maynej/Grua-Portuaria-Stemfie/Imatges/Carret28BYJ-48.png

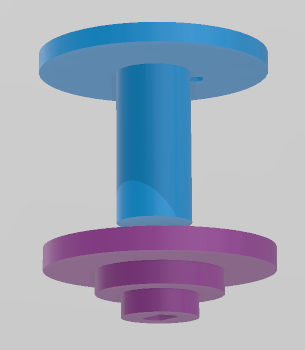
Imatges/Carret28BYJ-48.png
