maynej/Grua-Portuaria-Stemfie/Imatges/IMG_20220824_123127_317.jpg

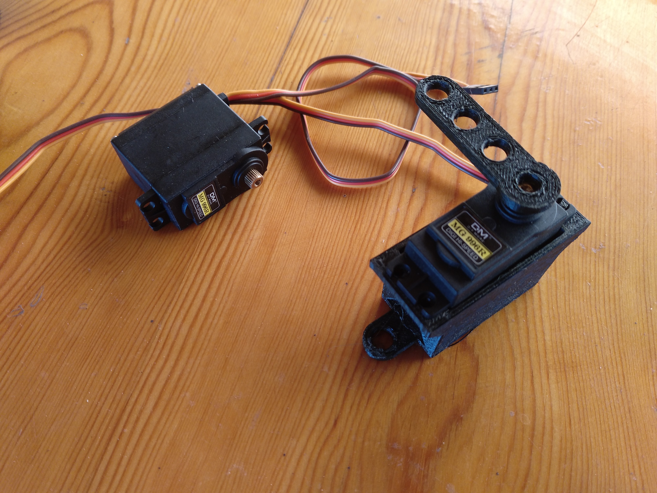
Imatges/IMG_20220824_123127_317.jpg
