maynej/Grua-Portuaria-Stemfie/STL/Base/28BYJ-48_2H_Stemfie_x1.stl

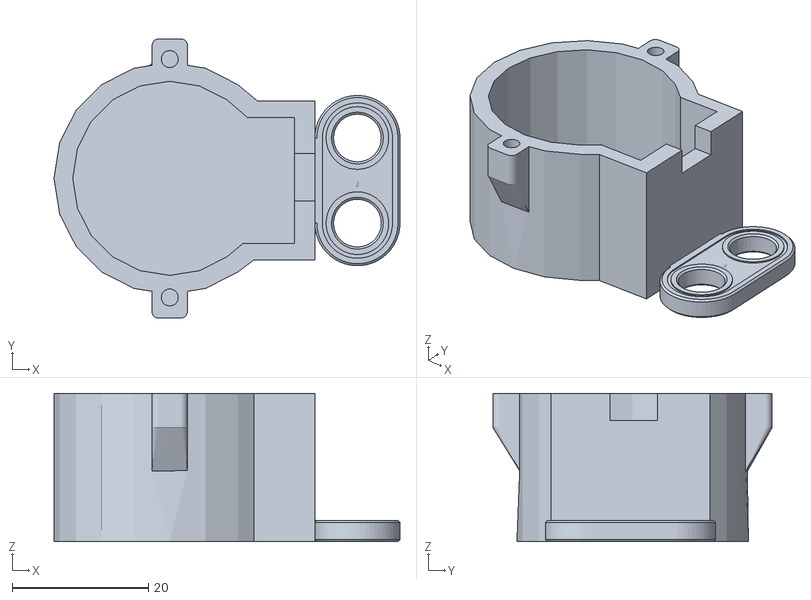
[picture p64: CAD file, 2022-09-06]
STL/Base/28BYJ-48_2H_Stemfie_x1.stl
50.8 x 41.0 x 21.8
