maynej/Grua-Portuaria-Stemfie/STL/PlataformaGiratoria/EngranatgeGrua_x1.stl

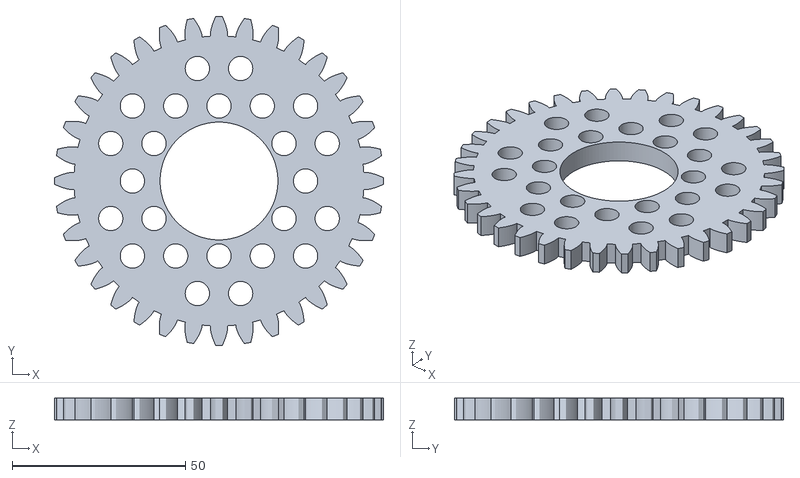
[picture p65: CAD file, 2022-09-06]
STL/PlataformaGiratoria/EngranatgeGrua_x1.stl
95.0 x 95.0 x 6.25
