maynej/Grua-Portuaria-Stemfie/STL/Ploma/PinBU03.75_x1.stl

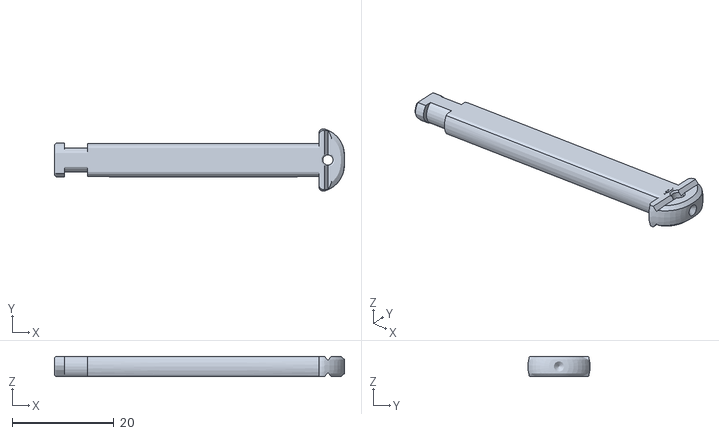
[picture p66: CAD file, 2022-09-06]
STL/Ploma/PinBU03.75_x1.stl
56.9 x 12.2 x 4.00
