maynej/Grua-Portuaria-Stemfie/STL/Base/Spool28BYJ-48_1.stl

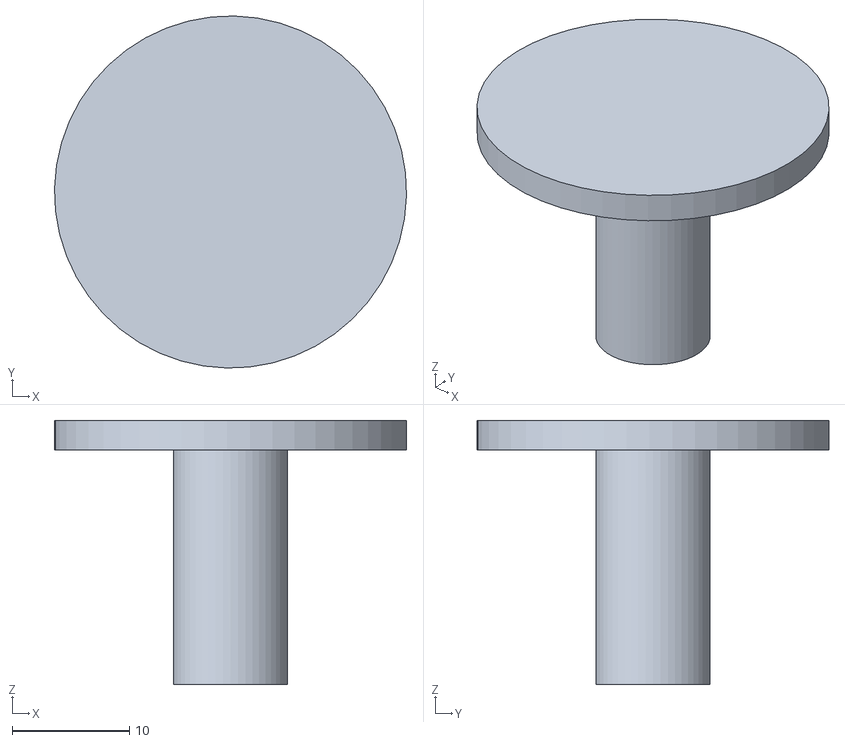
[picture p67: CAD file, 2022-09-06]
STL/Base/Spool28BYJ-48_1.stl
30.0 x 30.0 x 22.5
