maynej/Grua-Portuaria-Stemfie/STL/Ploma/Brace2_x8.stl

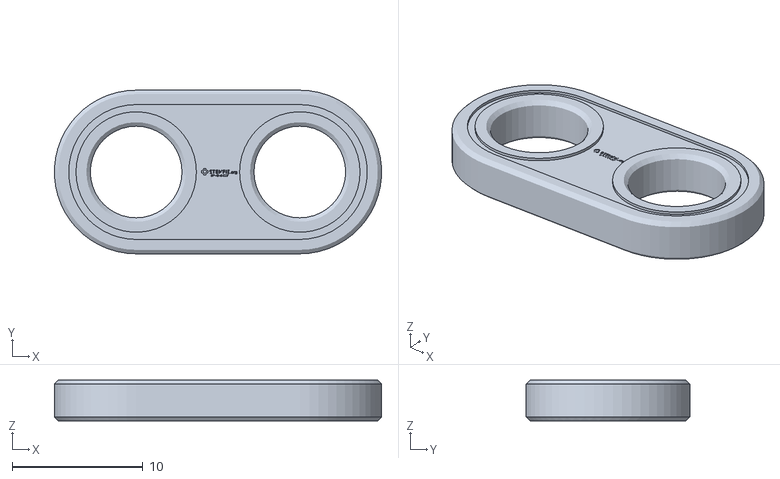
[picture p68: CAD file, 2022-09-06]
STL/Ploma/Brace2_x8.stl
25.0 x 12.5 x 3.12
