maynej/Grua-Portuaria-Stemfie/STL/Base/Brace18_x4.stl

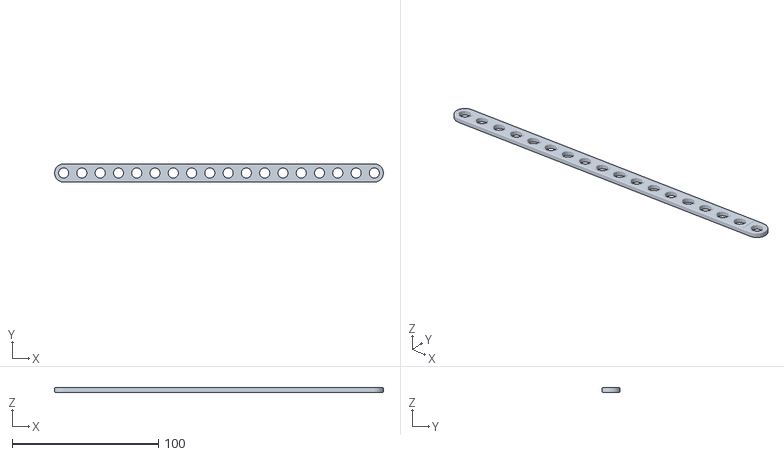
[picture p69: CAD file, 2022-09-06]
STL/Base/Brace18_x4.stl
225.0 x 12.5 x 3.12
