maynej/Grua-Portuaria-Stemfie/STL/Ploma/PulleyBU1.00_x3.stl

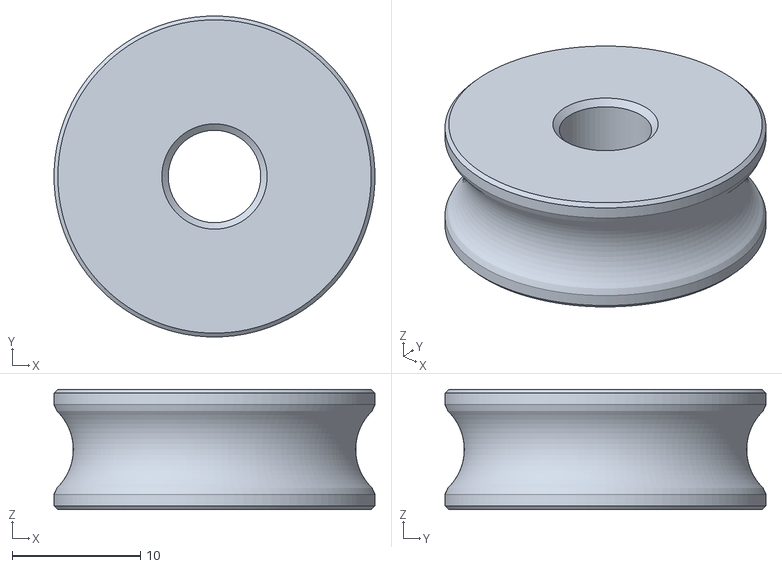
[picture p70: CAD file, 2022-09-06]
STL/Ploma/PulleyBU1.00_x3.stl
25.0 x 25.0 x 9.38
