maynej/Grua-Portuaria-Stemfie/STL/Base/Base8x10_x1.stl

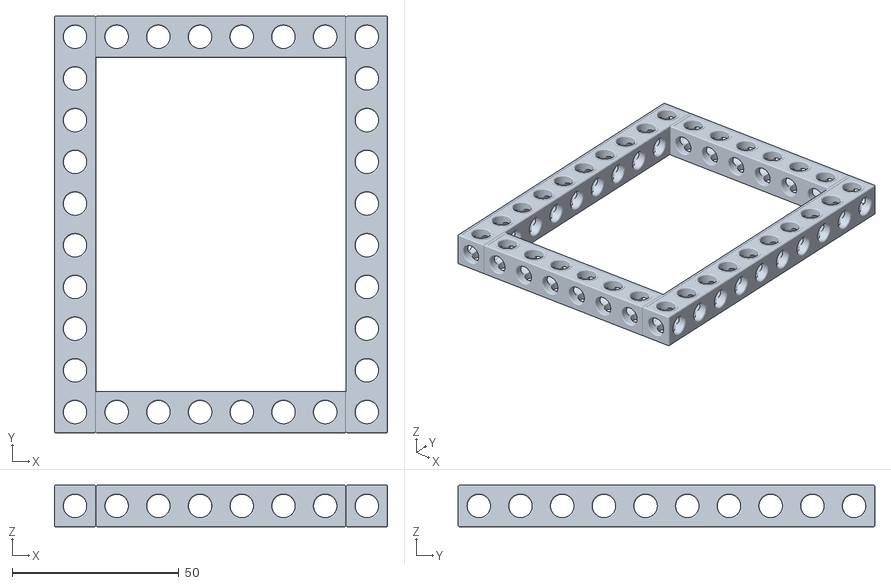
[picture p71: CAD file, 2022-09-06]
STL/Base/Base8x10_x1.stl
100.0 x 125.0 x 12.5
