maynej/Grua-Portuaria-Stemfie/STL/Ploma/Beam5_x2.stl

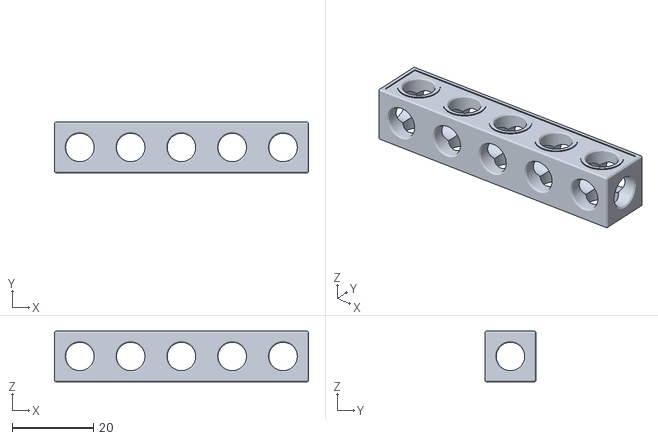
[picture p72: CAD file, 2022-09-06]
STL/Ploma/Beam5_x2.stl
62.5 x 12.5 x 12.5
