maynej/Grua-Portuaria-Stemfie/STL/Base/28BYJ-48_4H_Stemfie_x1.stl

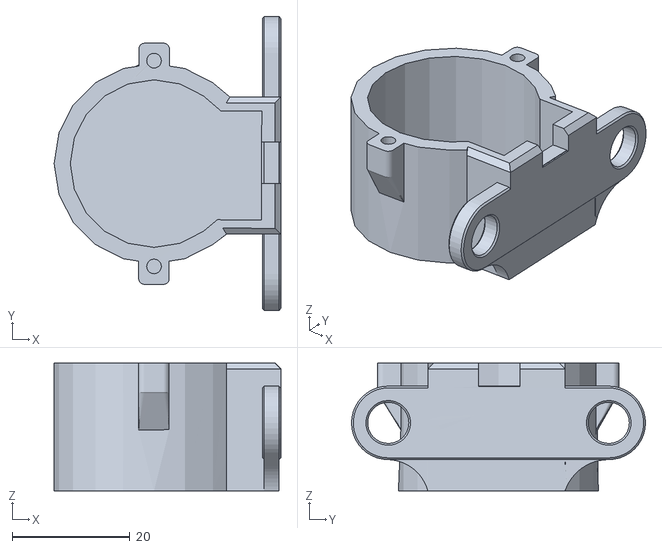
[picture p73: CAD file, 2022-09-06]
STL/Base/28BYJ-48_4H_Stemfie_x1.stl
38.6 x 50.0 x 21.8
