maynej/Grua-Portuaria-Stemfie/STL/Ploma/ServoMG966_V3_x2.stl

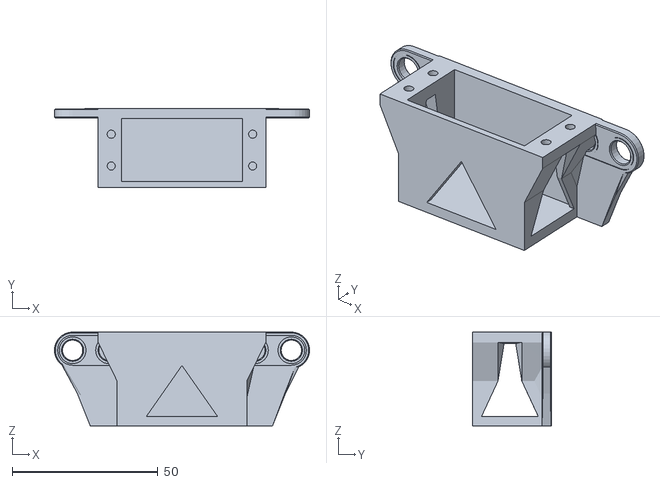
[picture p74: CAD file, 2022-09-06]
STL/Ploma/ServoMG966_V3_x2.stl
87.4 x 26.9 x 32.2
