maynej/Grua-Portuaria-Stemfie/STL/Base/Arandela2.5mm_x4.stl

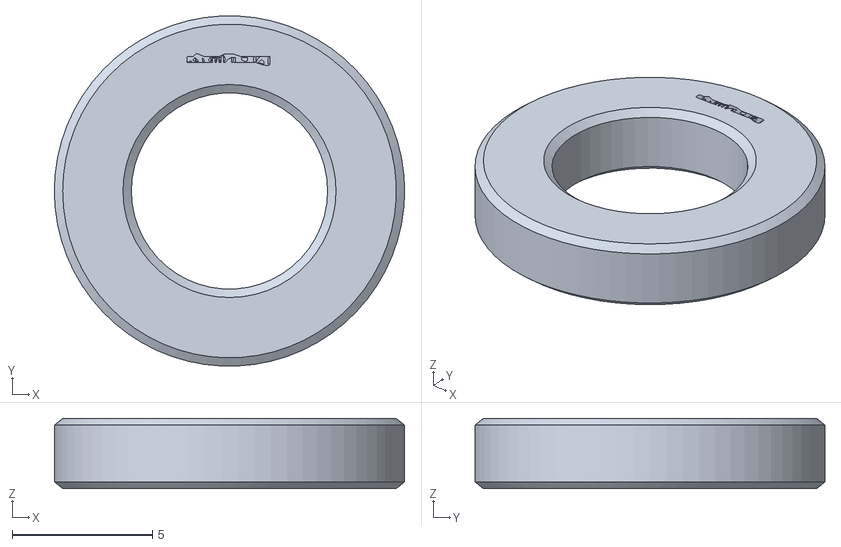
[picture p75: CAD file, 2022-09-06]
STL/Base/Arandela2.5mm_x4.stl
12.5 x 12.5 x 2.51
