maynej/Grua-Portuaria-Stemfie/STL/Base/Gear28BYJ-48_130mm_x1.stl

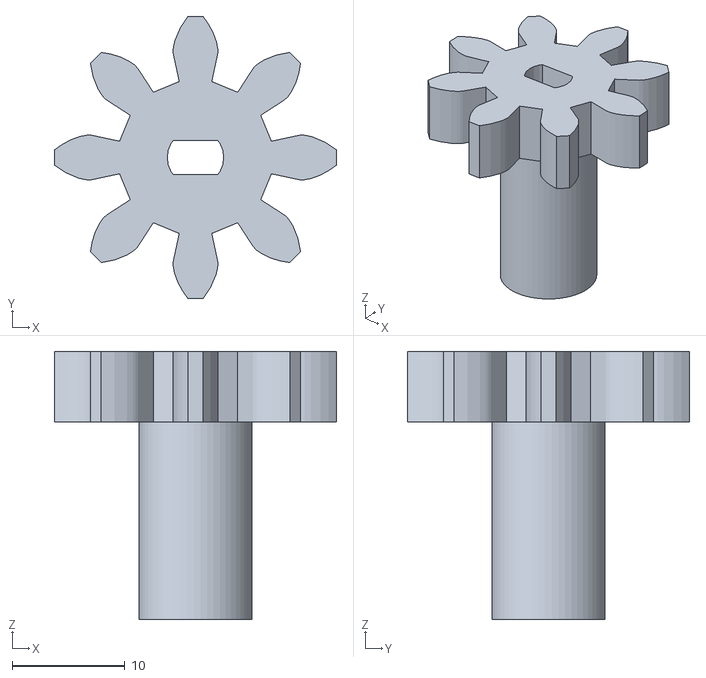
[picture p76: CAD file, 2022-09-06]
STL/Base/Gear28BYJ-48_130mm_x1.stl
25.0 x 25.0 x 23.8
