maynej/Grua-Portuaria-Stemfie/STL/Base/Brace13_x4.stl

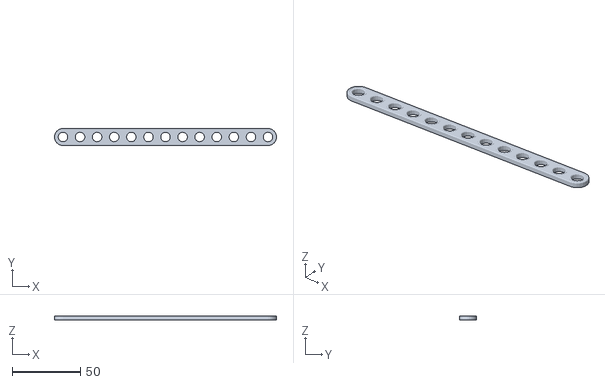
[picture p77: CAD file, 2022-09-06]
STL/Base/Brace13_x4.stl
162.4 x 12.5 x 3.12
