maynej/Grua-Portuaria-Stemfie/STL/Base/STR_STD_BRM-4x3_x1.stl

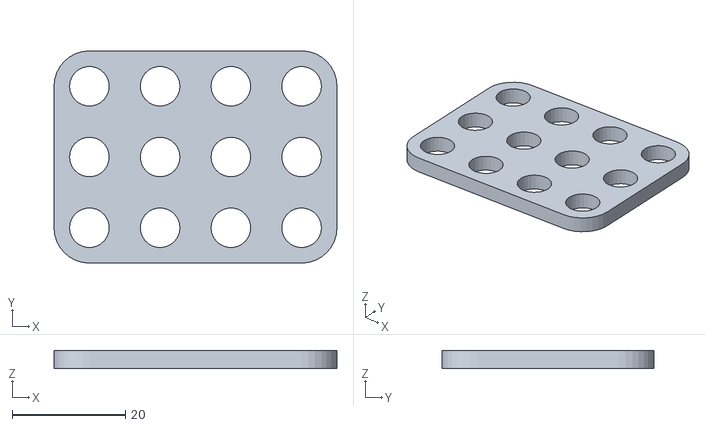
[picture p78: CAD file, 2022-09-06]
STL/Base/STR_STD_BRM-4x3_x1.stl
50.0 x 37.5 x 3.25
