maynej/Grua-Portuaria-Stemfie/STL/Ploma/Brace4_x6.stl

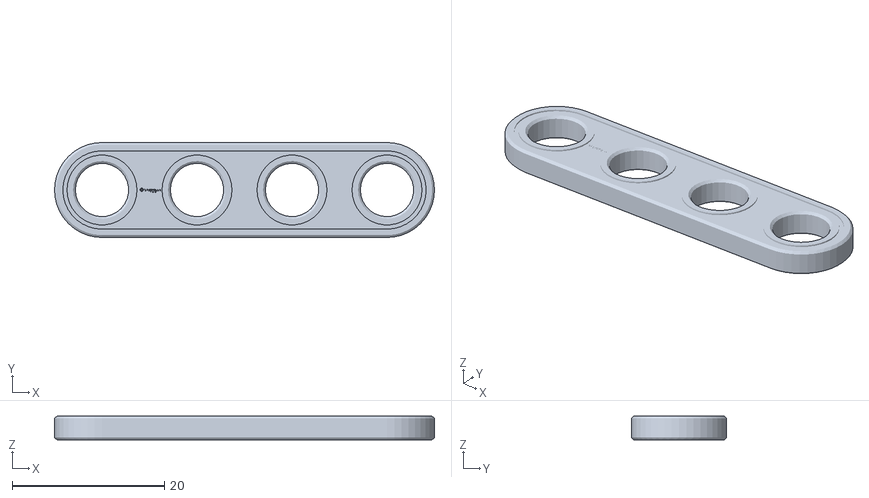
[picture p79: CAD file, 2022-09-06]
STL/Ploma/Brace4_x6.stl
50.0 x 12.5 x 3.12
