maynej/Grua-Portuaria-Stemfie/STL/Ploma/Brace6_x3.stl

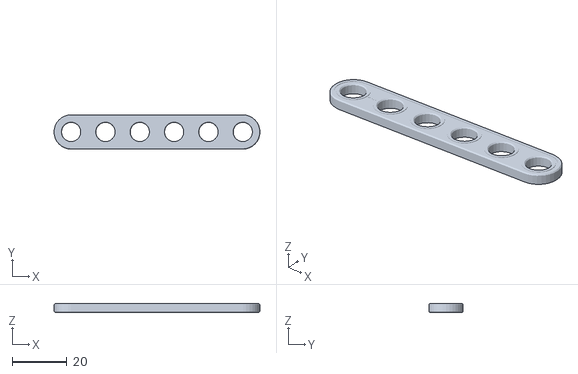
[picture p80: CAD file, 2022-09-06]
STL/Ploma/Brace6_x3.stl
75.0 x 12.5 x 3.12
