maynej/Grua-Portuaria-Stemfie/STL/Ploma/PinBU02.50_x4.stl

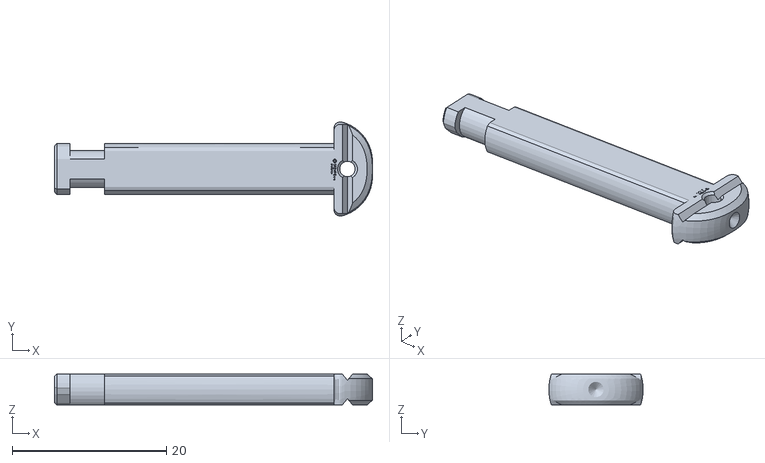
[picture p81: CAD file, 2022-09-06]
STL/Ploma/PinBU02.50_x4.stl
41.2 x 12.2 x 4.00
