maynej/Grua-Portuaria-Stemfie/STL/Ploma/Beam6x2_x1.stl

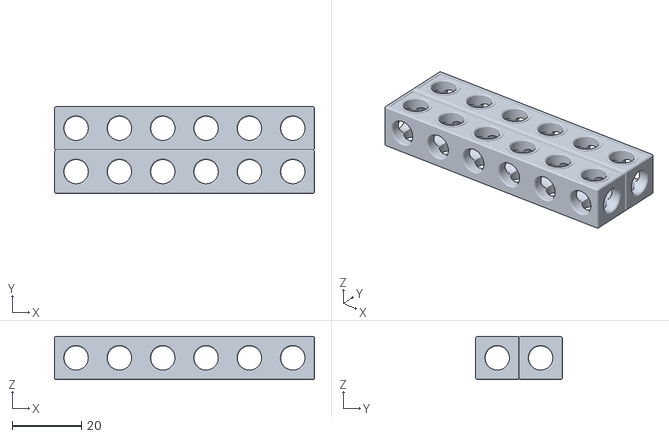
[picture p82: CAD file, 2022-09-06]
STL/Ploma/Beam6x2_x1.stl
75.0 x 25.0 x 12.5
