maynej/Grua-Portuaria-Stemfie/STL/Ploma/Brace12_x2.stl

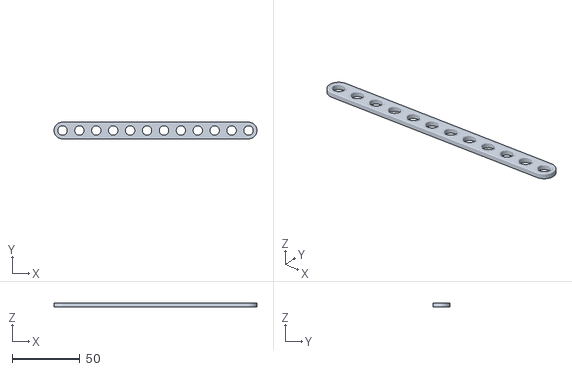
[picture p83: CAD file, 2022-09-06]
STL/Ploma/Brace12_x2.stl
150.0 x 12.5 x 3.12
