maynej/Grua-Portuaria-Stemfie/STL/Ploma/PinBU05.75_x1.stl

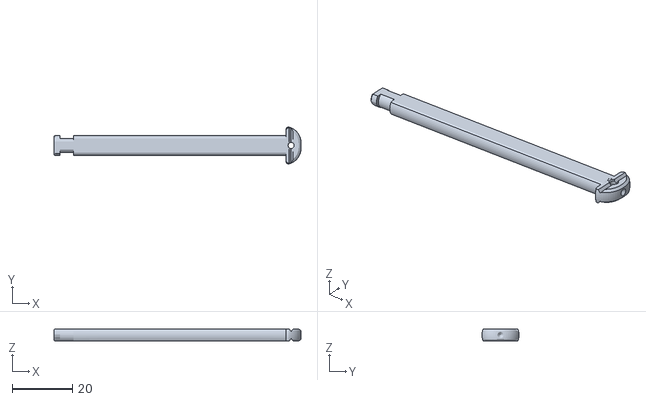
[picture p84: CAD file, 2022-09-06]
STL/Ploma/PinBU05.75_x1.stl
81.9 x 12.3 x 4.00
