maynej/Grua-Portuaria-Stemfie/STL/Ploma/PinBU01.75_x4.stl

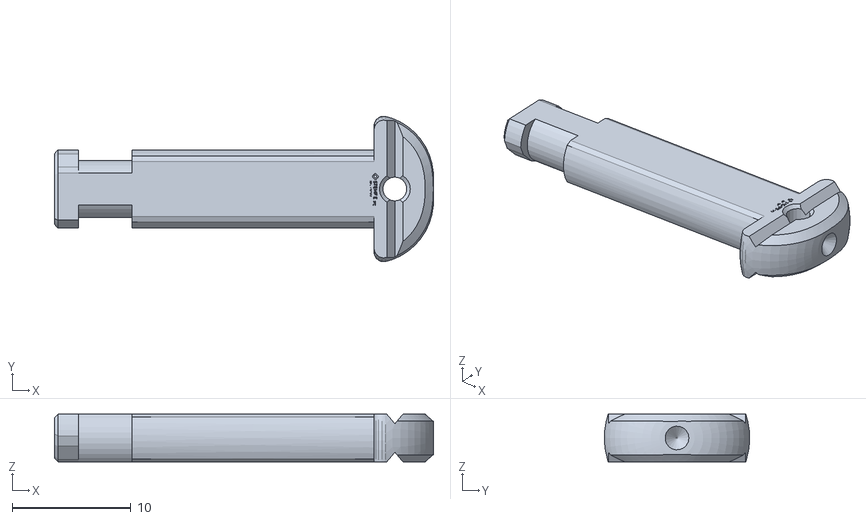
[picture p85: CAD file, 2022-09-06]
STL/Ploma/PinBU01.75_x4.stl
31.9 x 12.2 x 4.00
