maynej/Grua-Portuaria-Stemfie/STL/Ploma/Beam14_x3.stl

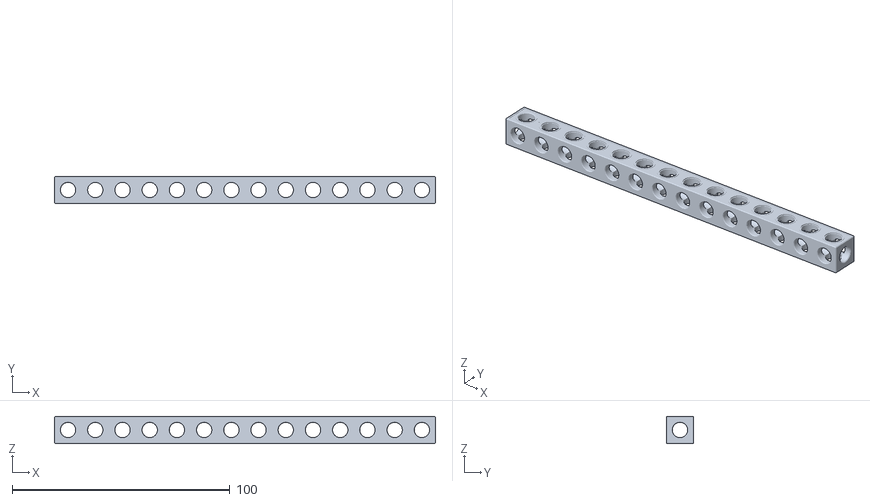
[picture p86: CAD file, 2022-09-06]
STL/Ploma/Beam14_x3.stl
175.0 x 12.5 x 12.5
