maynej/Grua-Portuaria-Stemfie/STL/Ploma/ServoMG996_Brace4_x2.stl

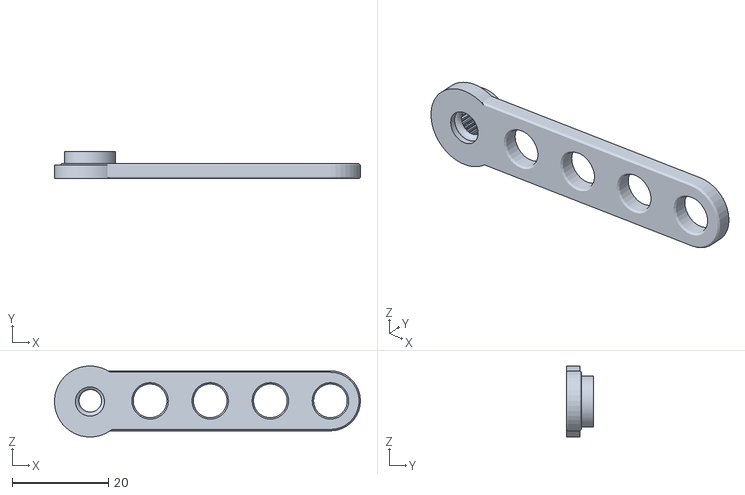
[picture p87: CAD file, 2022-09-06]
STL/Ploma/ServoMG996_Brace4_x2.stl
63.6 x 5.68 x 14.8
