maynej/Grua-Portuaria-Stemfie/STL/Ploma/NutFixed_x17.stl

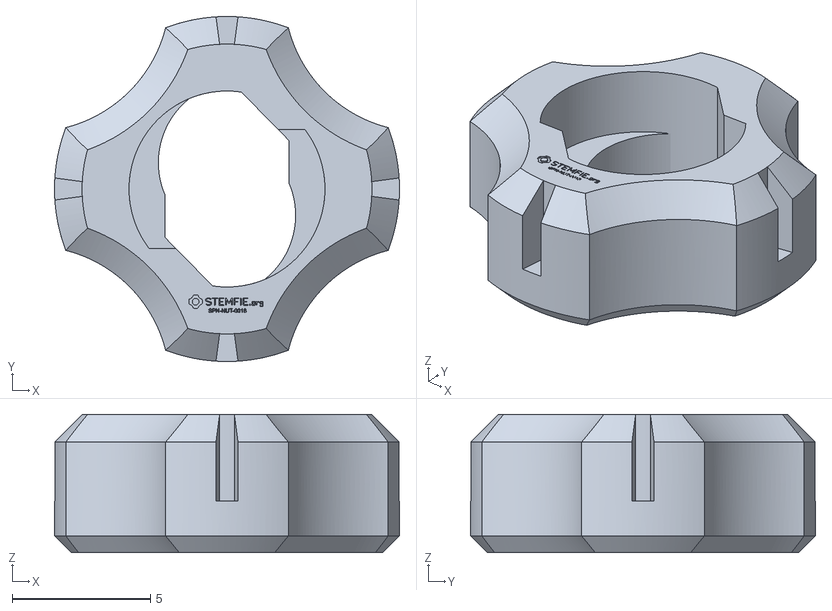
[picture p88: CAD file, 2022-09-06]
STL/Ploma/NutFixed_x17.stl
12.5 x 12.5 x 5.00
