maynej/Grua-Portuaria-Stemfie/STL/Ploma/Beam3_x1.stl

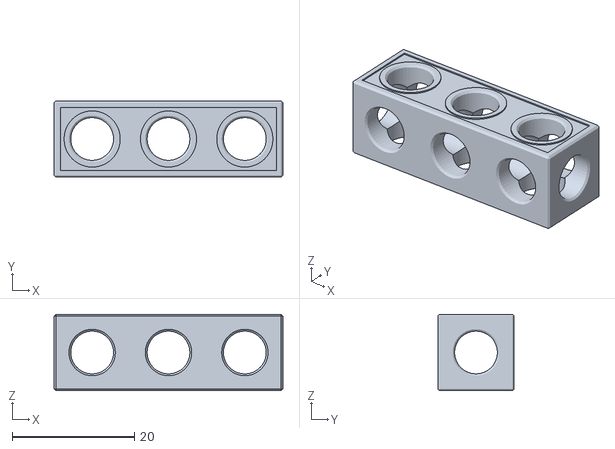
[picture p89: CAD file, 2022-09-06]
STL/Ploma/Beam3_x1.stl
37.5 x 12.5 x 12.5
