maynej/Grua-Portuaria-Stemfie/STL/Ploma/Beam18_x2.stl

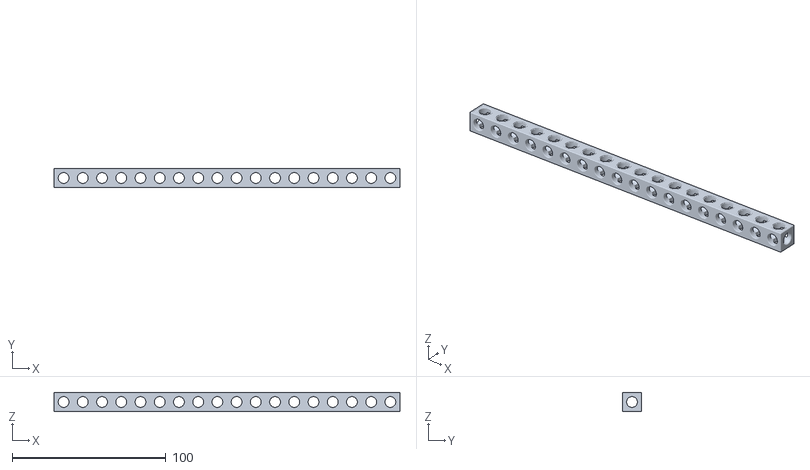
[picture p90: CAD file, 2022-09-06]
STL/Ploma/Beam18_x2.stl
225.0 x 12.5 x 12.5
