maynej/Grua-Portuaria-Stemfie/STL/Ploma/PinBU01.50_x16.stl

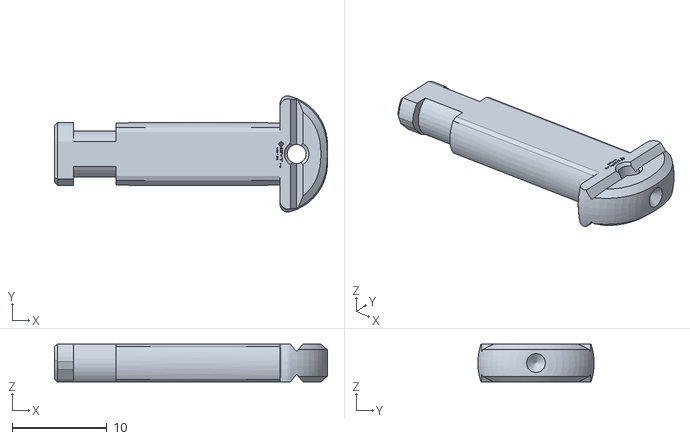
[picture p91: CAD file, 2022-09-06]
STL/Ploma/PinBU01.50_x16.stl
28.8 x 12.3 x 4.00
