maynej/Grua-Portuaria-Stemfie/STL/Ploma/Beam4_x1.stl

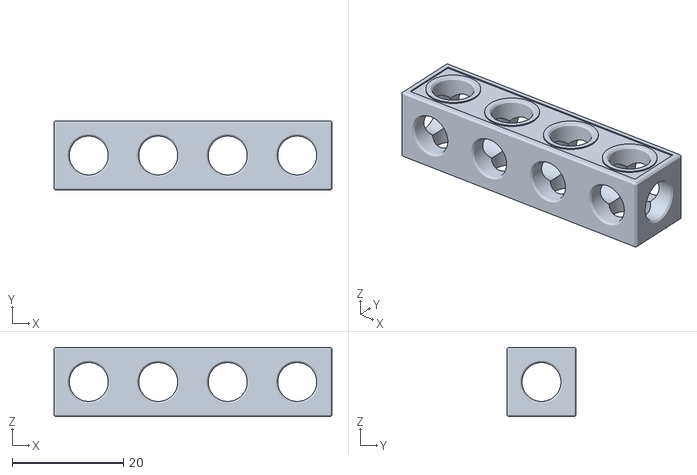
[picture p92: CAD file, 2022-09-06]
STL/Ploma/Beam4_x1.stl
50.0 x 12.5 x 12.5
