maynej/Grua-Portuaria-Stemfie/STL/Ploma/PinBU01.25_x4.stl

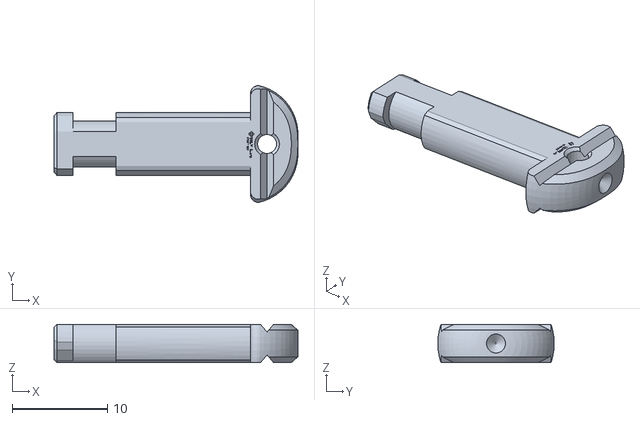
[picture p93: CAD file, 2022-09-06]
STL/Ploma/PinBU01.25_x4.stl
25.6 x 12.2 x 4.00
