maynej/Grua-Portuaria-Stemfie/STL/Ploma/PinBU00.50x2.stl

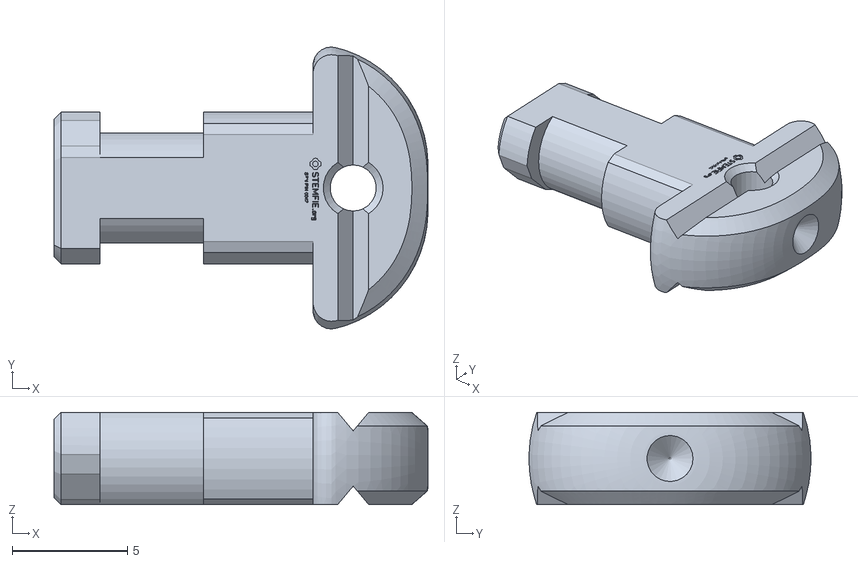
[picture p94: CAD file, 2022-09-06]
STL/Ploma/PinBU00.50x2.stl
16.2 x 12.3 x 4.00
