maynej/Grua-Portuaria-Stemfie/STL/Ploma/Brace8_x1.stl

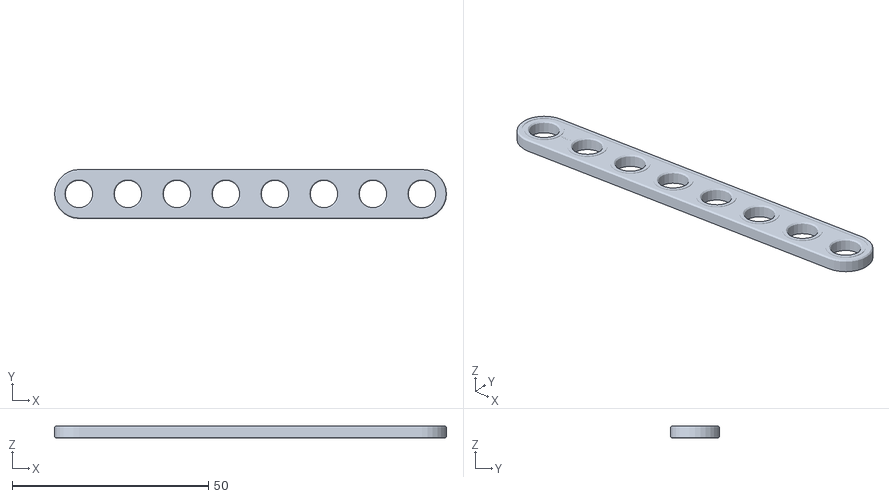
[picture p95: CAD file, 2022-09-06]
STL/Ploma/Brace8_x1.stl
100.0 x 12.5 x 3.12
