maynej/Grua-Portuaria-Stemfie/STL/Ploma/Beam7T3_x2.stl

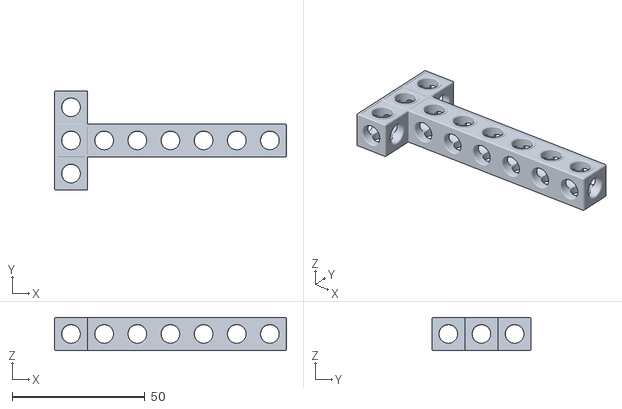
[picture p96: CAD file, 2022-09-06]
STL/Ploma/Beam7T3_x2.stl
87.5 x 37.5 x 12.5
